tymroche/LaserTag/Firmware/Server/Host-Server.h

/**
 * @file Host-Server.h
 * @author Alfonso Landaverde, Tyler Roche
 * @date 4/15/2026
 * @version 1.0
 *
 * @brief Definitions of Host Server and HTML.
 *
 * This file defines all variables, structs, and functions necessary for Laser Tag Game.
 * 
 * @see config.h for the hardware definitions like GPIO mapping
 */

#ifndef HOST_SERVER_H
#define HOST_SERVER_H

#include <WiFi.h>
#define MAX_PLAYERS 4 //not a hard max, just defined for our demo functionality


//global variables start

extern String header;
extern String gameMode;
extern String statusMessage;

extern const uint8_t STARTING_HP;
extern const int16_t STARTING_FFA_POINTS;
extern const int16_t FFA_HIT_GAIN;
extern const int16_t FFA_HIT_LOSS;
extern const uint16_t DEFAULT_FFA_SECONDS;

extern const char* ssid;
extern const char* password;

extern WiFiServer webServer;
extern WiFiServer deviceServer;

/**
 * @brief Player Struct used to keep track of identifying information and game-state variables.
 */
struct Player {
  String name;
  String vestDeviceId;
  String playerId;
  uint8_t hp;
  int16_t score;
  bool active;
  bool alive;
  bool canShoot;
};

extern Player players[MAX_PLAYERS];
extern WiFiClient deviceClients[MAX_PLAYERS];

extern uint8_t rankedPlayers[MAX_PLAYERS];
extern uint8_t rankedCount;

extern uint16_t ffaDurationSeconds;
extern bool ffaTimerRunning;
extern bool duelsGameRunning;
extern bool roundOver;
extern String roundOverMessage;
extern unsigned long ffaStartMillis;


//global variables end

/**
 * @brief Decodes URL characters from browser request.
 * @param s URL-encoded string to decode.
 * @return Decoded, trimmed string.
 */
String decodeUrl(String s);

/**
 * @brief Extracts query parameter from HTTP GET request.
 * @param req HTTP request string.
 * @param key Query parameter to extract.
 * @return Decoded value of the requested parameter.
 */
String getQueryValue(String req, String key);

/*
  Convert a player slot number to the assigned IR/player ID.
  slot 0 1
  slot 1 2
  slot 2 3
  slot 3 4
*/
/**
 * @brief Converts player slot index to assigned player ID for IR.
 * @param slot player slot index.
 * @return Player ID (1-4) for valid slots, or an empty string for an invalid slot.
 */
String slotToPlayerId(int8_t slot);

/**
 * @brief Find a player slot by vest ID.
 * @param vestDeviceId Vest ID.
 * @return Matching player slot or -1.
 */
int8_t findPlayerByVestDeviceId(String vestDeviceId);

/**
 * @brief Find a player slot by assigned game player ID.
 * @param playerId Assigned player ID.
 * @return Matching player slot index or -1.
 */
int8_t findPlayerByAssignedPlayerId(String playerId);

/**
 * @brief Finds the first unused player slot.
 * @return Index of the first free player slot, or -1 if the lobby is full.
 */
int8_t findOpenSlot();

/**
 * @brief Resets one player's stats for the current mode.
 * @param index Player slot index to reset.
 */
void resetPlayerForCurrentMode(int8_t index);

/**
 * @brief Resets all player records and closes any client connections.
 */
void resetAllPlayers();

/*UNDER CONSTRUCTION, WOULD LIKE TO HAVE TIMER ACTIVELY DISPLAY TIME*/

/**
 * @brief Computes the time remaining for Free For All timer.
 * @return Remaining timer value in seconds, or zero once the timer has expired.
 */
uint16_t getRemainingFFATime();

/**
 * @brief Formats seconds as minutes:seconds.
 * @param totalSeconds Total seconds.
 * @return Formatted string in M:SS form.
 */
String formatTime(uint16_t totalSeconds);

/**
 * @brief Send the current host state to one vest.
 * Includes the assigned PLAYERID that the vest should use in IR transmit.
 * @param index Player slot whose vest should receive the state update.
 */
void sendStateToPlayer(int8_t index);

/**
 * @brief Sends game state to every player slot.
 */
void sendStateToAllPlayers();

/**
 * @brief Removes one player from the lobby and disconnects any linked vest client.
 * @param index Player slot index to remove.
 */
void removePlayer(int8_t index);

/**
 * @brief Removes all player from lobby.
 */
void removeAllPlayers();

/**
 * @brief Compares two active player slots to determine scoreboard ordering.
 * @param a First player slot index to compare.
 * @param b Second player slot index to compare.
 * @return true if player a should rank above player b; otherwise false.
 */
bool ranksHigher(int8_t a, int8_t b);

/**
 * @brief Builds sorted player list used by scoreboard.
 */
void buildRankings();

/*
  Start, stop, reset FFA timer.
*/

/**
 * @brief Starts Free For All timer and broadcasts updated state.
 */
void startFFATimer();

/**
 * @brief Stops Free For All timer and broadcasts updated state.
 */
void stopFFATimer();

/**
 * @brief Resets the Free For All timer state and broadcasts updated state.
 */
void resetFFATimer();

/**
 * @brief Starts Duels game and broadcasts updated state.
 */
void startDuelsGame();

/**
 * @brief Stops Duels game and broadcasts updated state.
 */
void stopDuelsGame();

/**
 * @brief Changes current game mode and resets all active players.
 * @param newMode New game mode string to apply.
 */
void setGameMode(String newMode);

/**
 * @brief Registers a newly connected vest or reconnects an existing vest to a player slot.
 * @param vestDeviceId Unique device identifier reported by the vest.
 * @param name Player name associated with the vest.
 * @param client Connected TCP client for that vest.
 */
void registerVest(String vestDeviceId, String name, WiFiClient client);

/**
 * @brief Processes a hit report sent by a vest and applies the appropriate scoring or HP changes.
 * @param targetIndex Player slot index of the vest that reported being hit.
 * @param attackerId Assigned player ID of the attacker IR.
 * @note Process one hit report. e.g. HIT 2
 */
void processHitReport(int8_t targetIndex, String attackerId);

/**
 * @brief Accepts new vest TCP connections and processes messages from connected vests.
 * @note Accept new vest connections and process vest messages.
 *       HELLO <vestDeviceId> <playerName>
 *       HIT <attackerPlayerId>
 */
void handleDeviceConnections();

/**
 * @brief Processes a browser request.
 * @param req HTTP request string to inspect for actions.
 */
void handleBrowserAction(String req);

/**
 * @brief Sends an HTTP redirect response back to the browser homepage.
 * clears url as well to prevent duplicate actions.
 * @param client Connected web client to respond to.
 */
void redirectToHome(WiFiClient& client);

/**
 * @brief Generates and sends the current control page and scoreboard HTML to a browser client.
 * @param client Connected web client to respond to.
 */
void serveWebPage(WiFiClient& client);

/**
 * @brief Accepts browser connections, parses requests, and serves html page.
 */
void handleWebClients();

/**
 * @brief Clears the current round-over state and winner message.
 */
void clearRoundOverState();

/**
 * @brief Checks whether the current round has ended and updates round-over state.
 * @return true if the round is over, otherwise false.
 */
bool isRoundOver();

/**
 * @brief Returns true when the current mode is actively running.
 * @return true if the current mode is in an active round; otherwise false.
 */
bool isGameRunning();

/**
 * @brief Returns the timer value that should be sent to vest clients.
 * @return Remaining FFA time during Free For All, 1 during active Duels, otherwise 0.
 */
uint16_t getTimerValueForState();

/**
 * @brief Applies current mode state to one player's alive/canShoot fields.
 * @param index Player slot index to update.
 */
void syncPlayerRoundState(int8_t index);

/**
 * @brief Applies current mode state to all active players.
 */
void syncAllPlayersRoundState();

/**
 * @brief Builds the STATE line sent to one vest client.
 * @param index Player slot index whose state is being serialized.
 * @return Complete STATE message line.
 * @note  Text protocol sent to vest:
 *        STATE PLAYERID=<id> MODE=<mode> ALIVE=<0/1> CANSHOOT=<0/1> HP=<hp> SCORE=<score> TIMER=<seconds/flag>
 */
String buildStateMessage(int8_t index);

/**
 * @brief Reads the HELLO line from a newly connected vest.
 * @param client Newly connected TCP client.
 * @return Parsed HELLO line, or an empty string on timeout/failure.
 */
String readHelloLine(WiFiClient& client);

/**
 * @brief Handles one new vest connection if available.
 */
void handleNewDeviceConnection();

/**
 * @brief Handles incoming messages from already connected vest clients.
 */
void handleExistingDeviceMessages();

/**
 * @brief Removes vest clients that have disconnected from the host.
 */
void cleanupDisconnectedClients();

/**
 * @brief Returns whether a browser request should be redirected after action processing.
 * @param requestLine First line of the HTTP request.
 * @return true if the request mutates state and should redirect; otherwise false.
 */
bool isActionRequest(String requestLine);

/**
 * @brief clears all stale tcp requests so that they don't instantly report at the start of a new round
 */
void clearPendingDeviceMessages();

#endif
